hendrieepis/Board-AVR-LAB-2026-V1/assets/image-20260628081357848.png

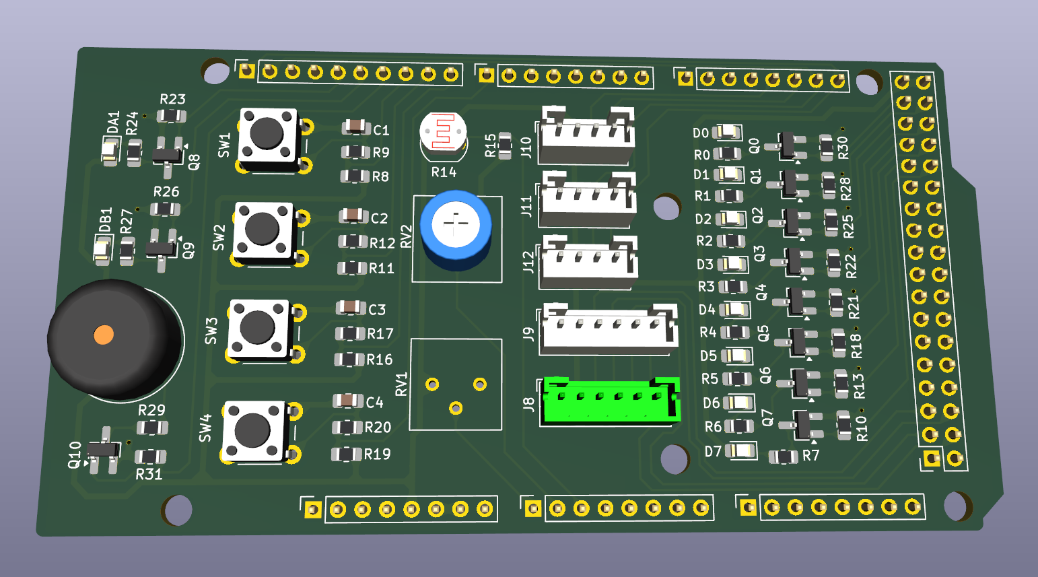
assets/image-20260628081357848.png
