hendrieepis/Board-AVR-LAB-2026-V1/versiA/Bottom 3D.png

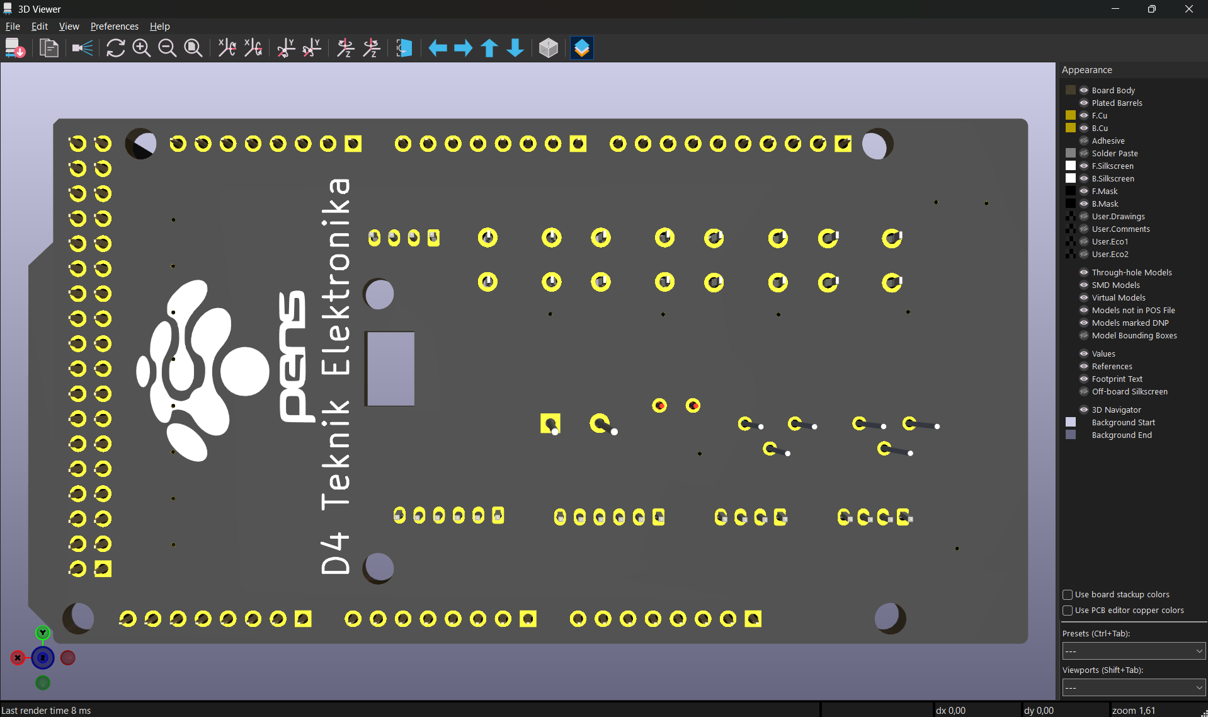
versiA/Bottom 3D.png
