hendrieepis/Board-AVR-LAB-2026-V1/versiA/Top3D.png

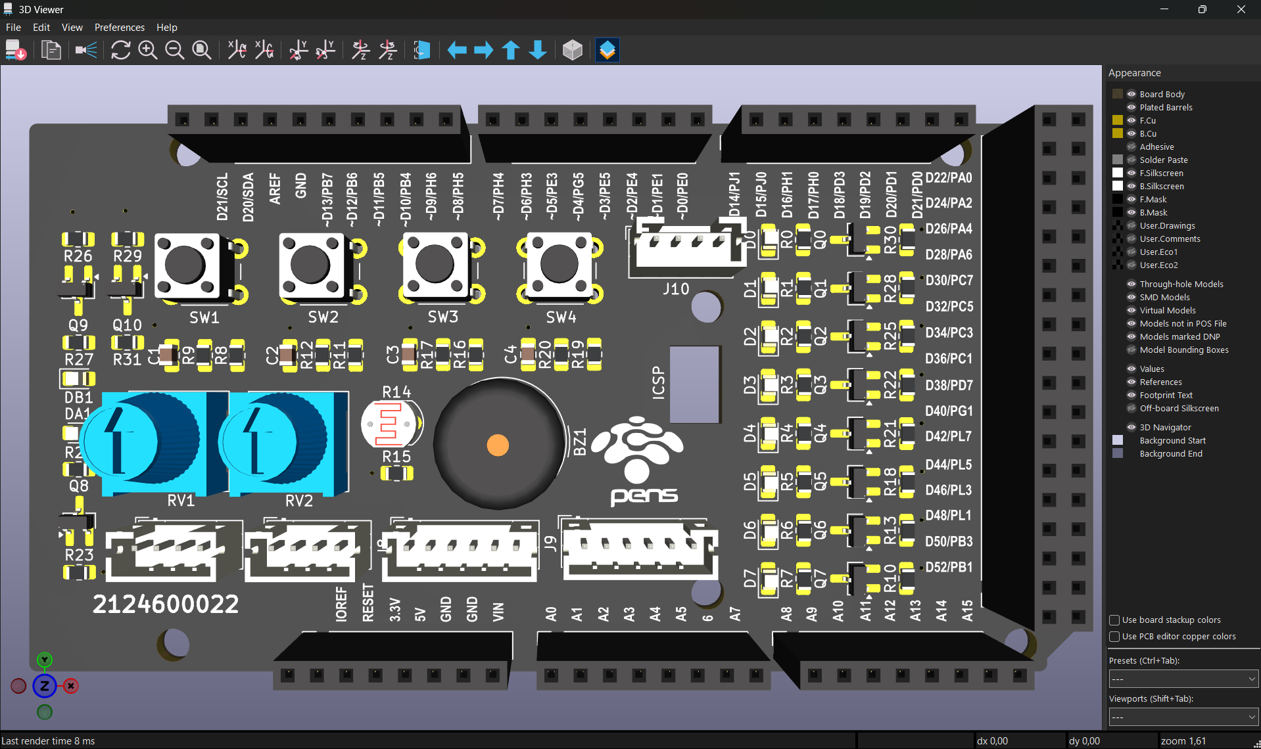
versiA/Top3D.png
