hendrieepis/Board-AVR-LAB-2026-V1/versiA/Top.png

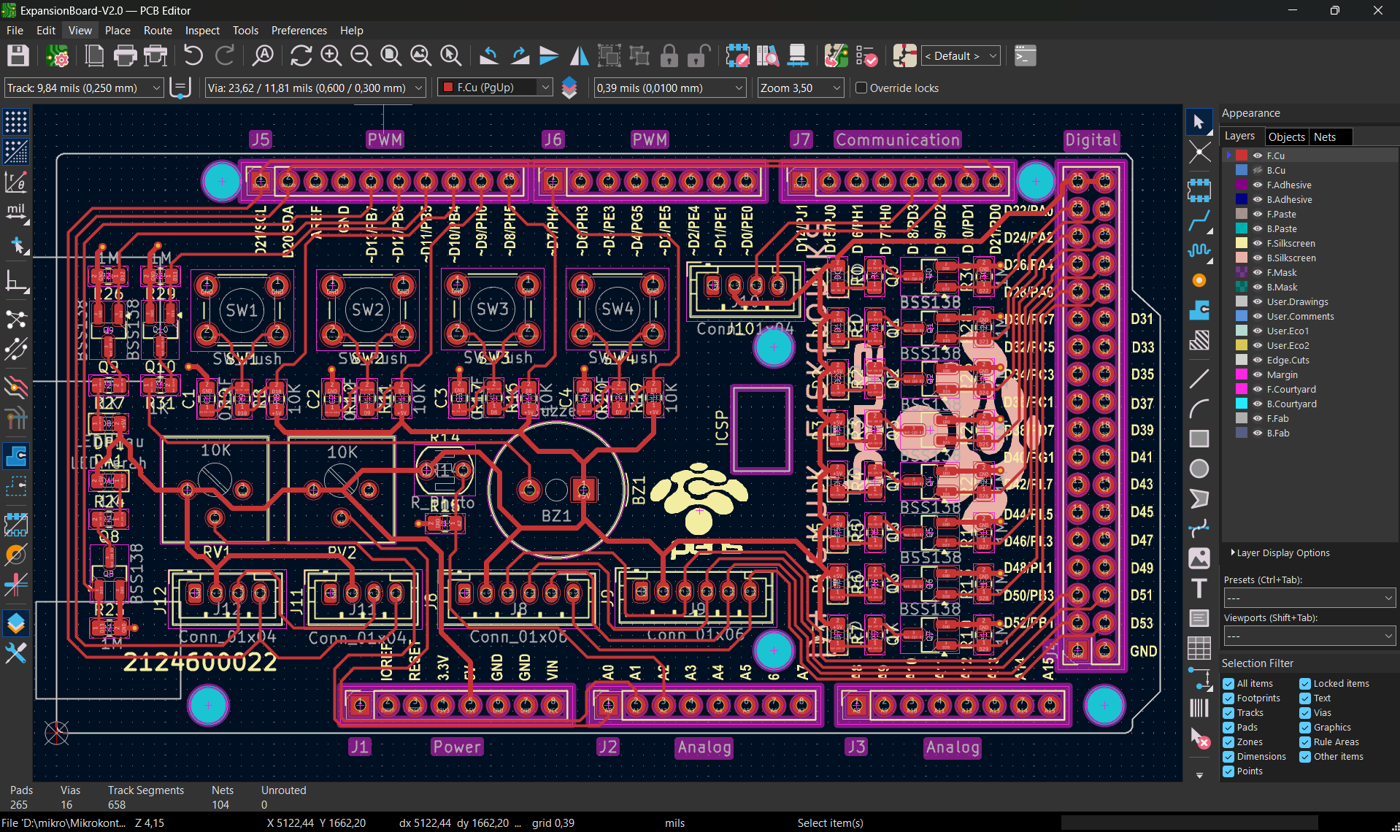
versiA/Top.png
