hendrieepis/Board-AVR-LAB-2026-V1/VersiB/BOTTOM LAYER.png

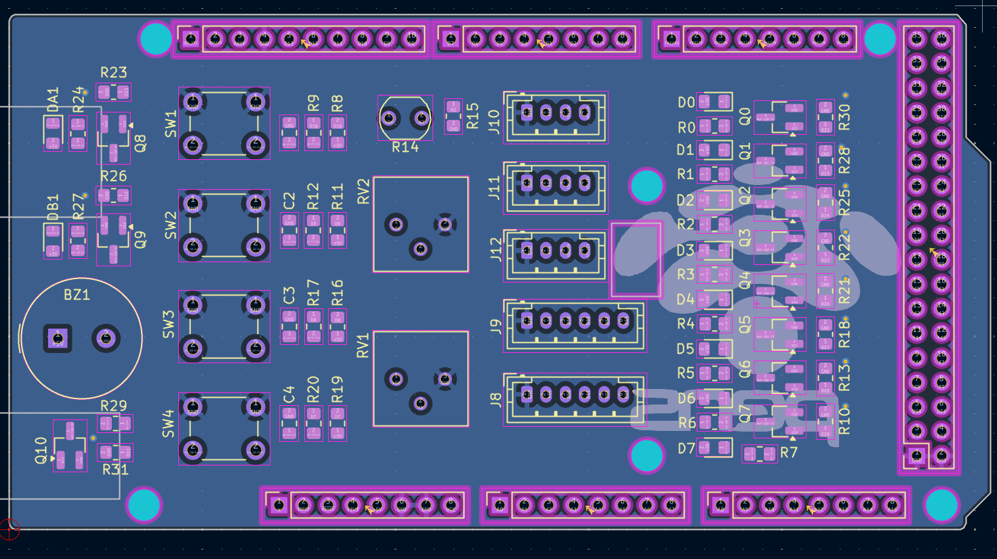
VersiB/BOTTOM LAYER.png
