hendrieepis/Board-AVR-LAB-2026-V1/VersiB/PCB1.png

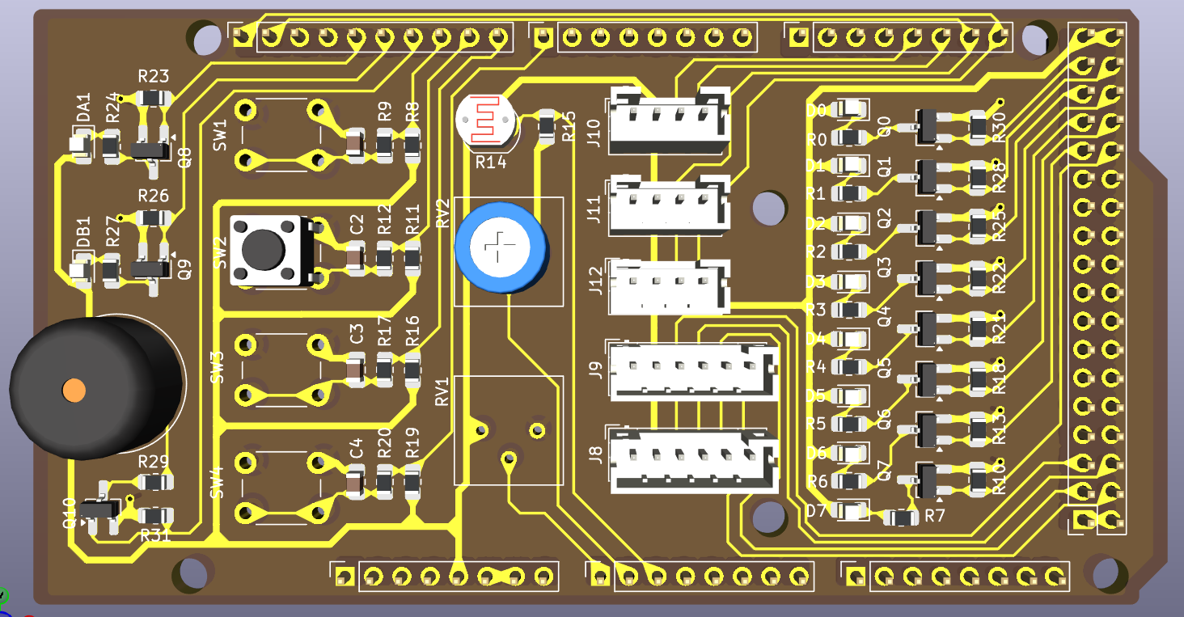
VersiB/PCB1.png
