hendrieepis/Board-AVR-LAB-2026-V1/VersiB/PCB.png

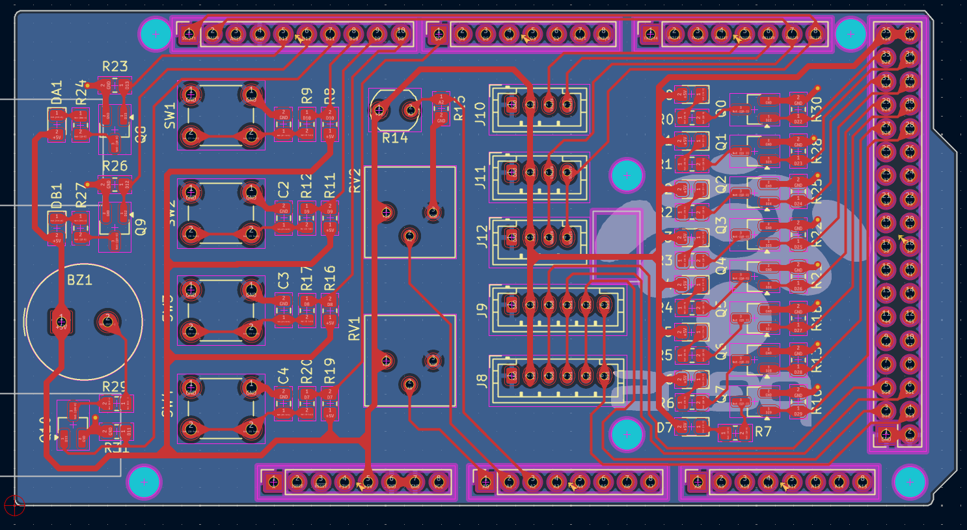
VersiB/PCB.png
