hendrieepis/Board-AVR-LAB-2026-V1/VersiB/TOP LAYER.png

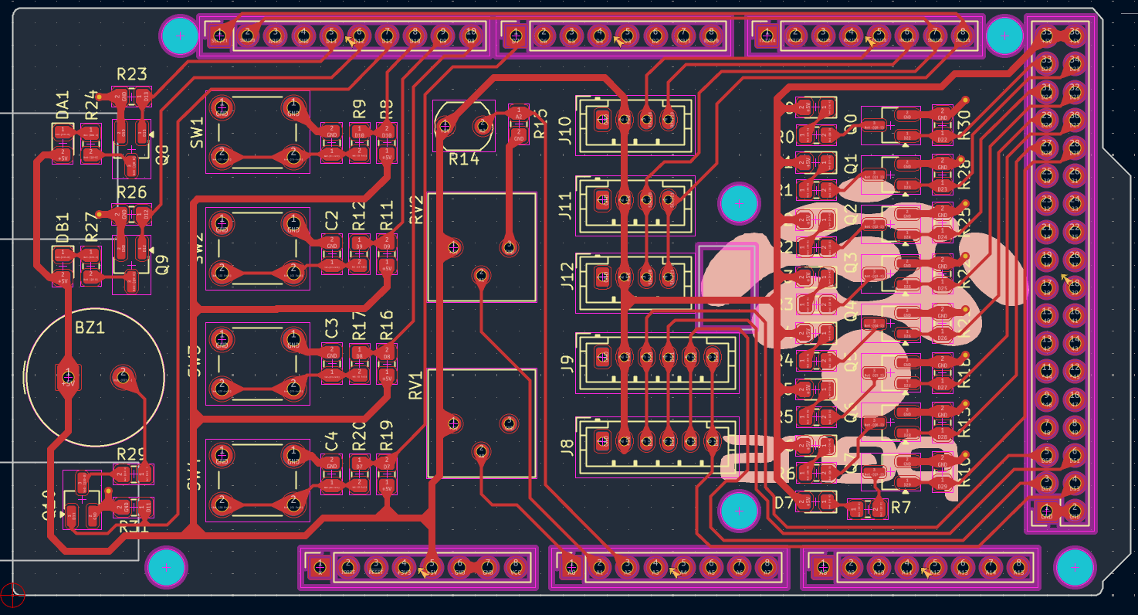
VersiB/TOP LAYER.png
